Jack53416/SoundLocalization/docs/pictures/ClientGuiDiagram.png

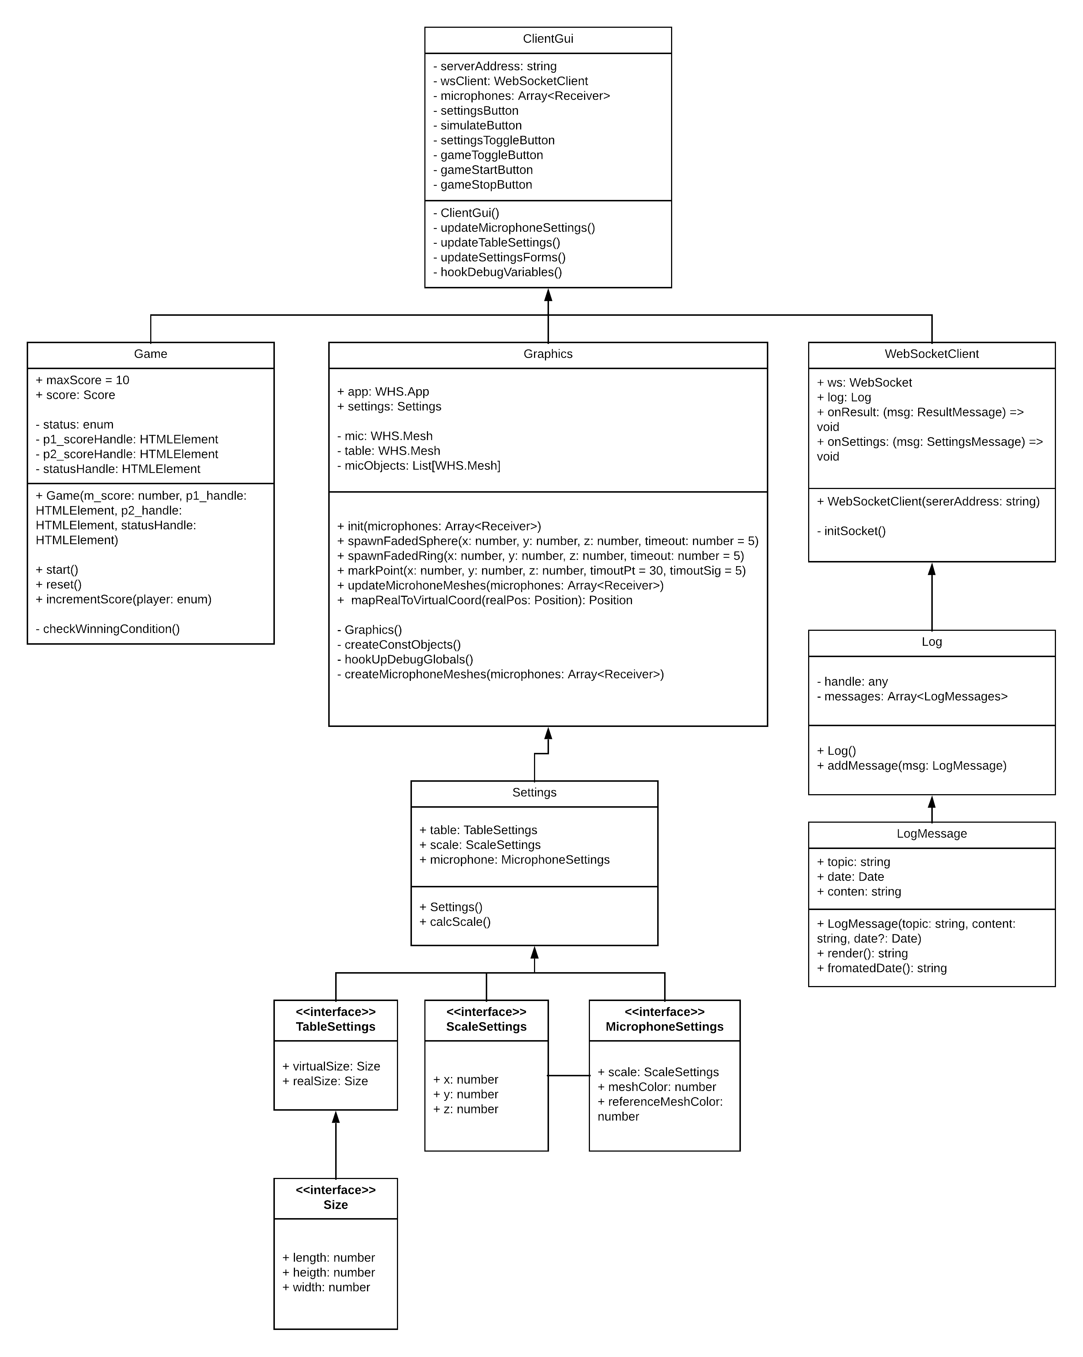
docs/pictures/ClientGuiDiagram.png
