Jack53416/SoundLocalization/docs/pictures/Device diagramV2.png

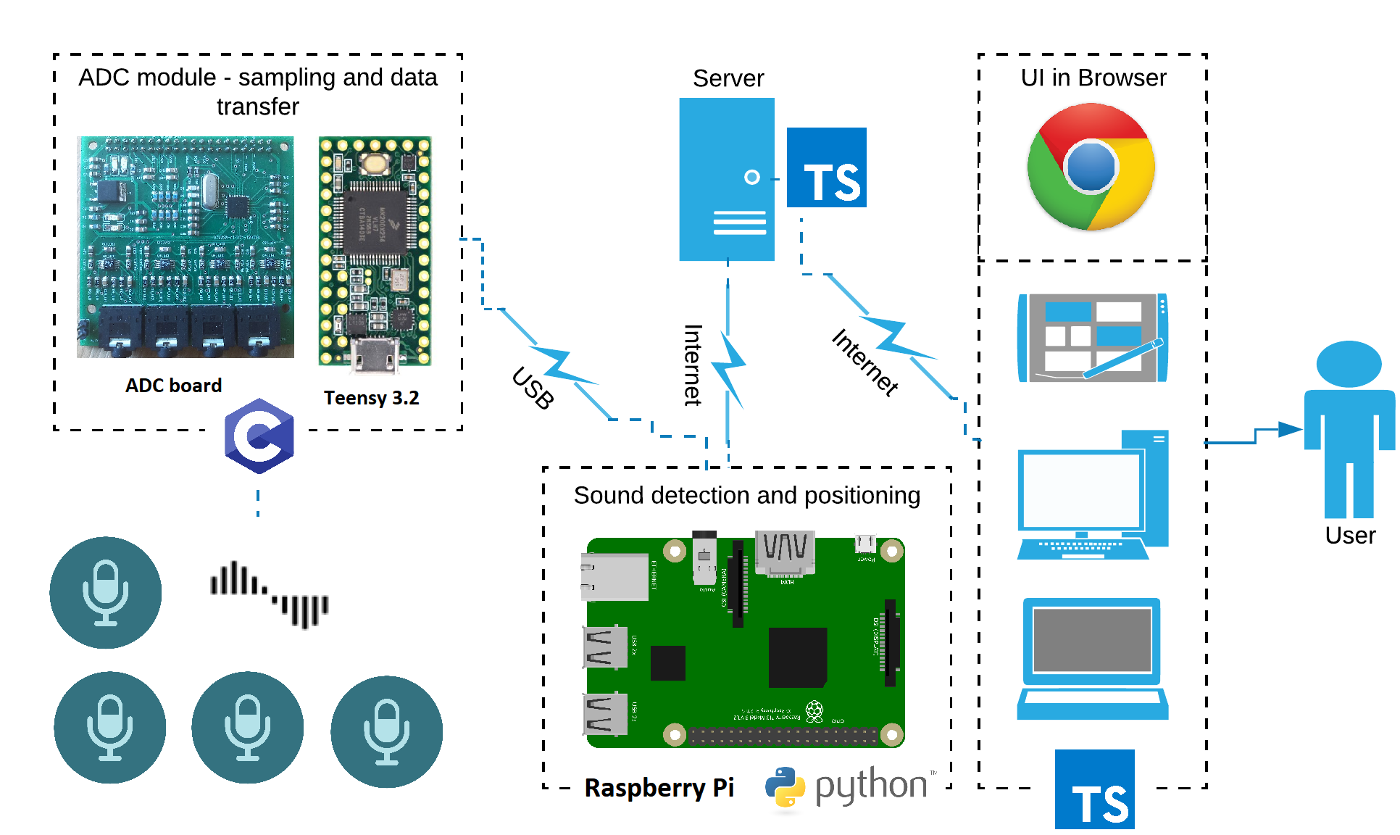
docs/pictures/Device diagramV2.png
