Jack53416/SoundLocalization/docs/pictures/gui-options.PNG

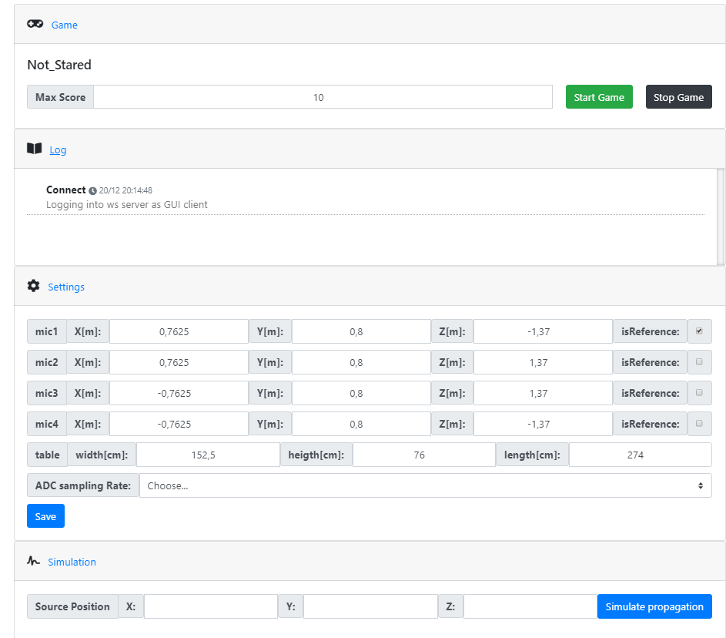
docs/pictures/gui-options.PNG
