Jack53416/SoundLocalization/docs/pictures/GUI.PNG

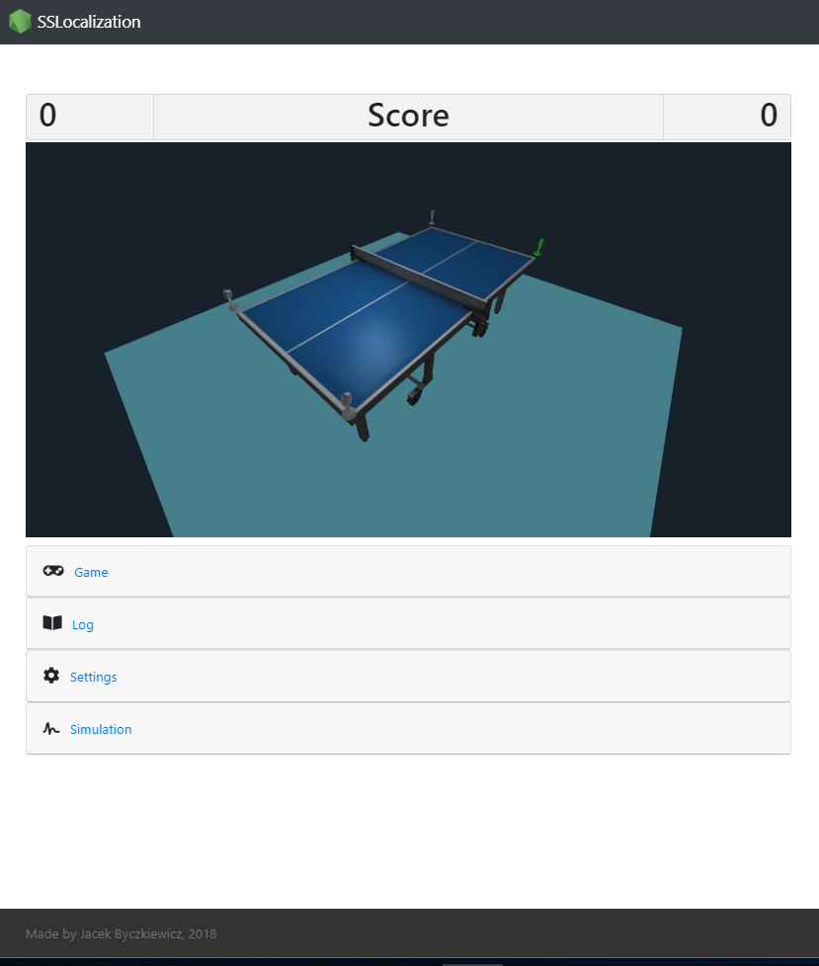
docs/pictures/GUI.PNG
