Jack53416/SoundLocalization/docs/pictures/IncomingMessagesDiagram.png

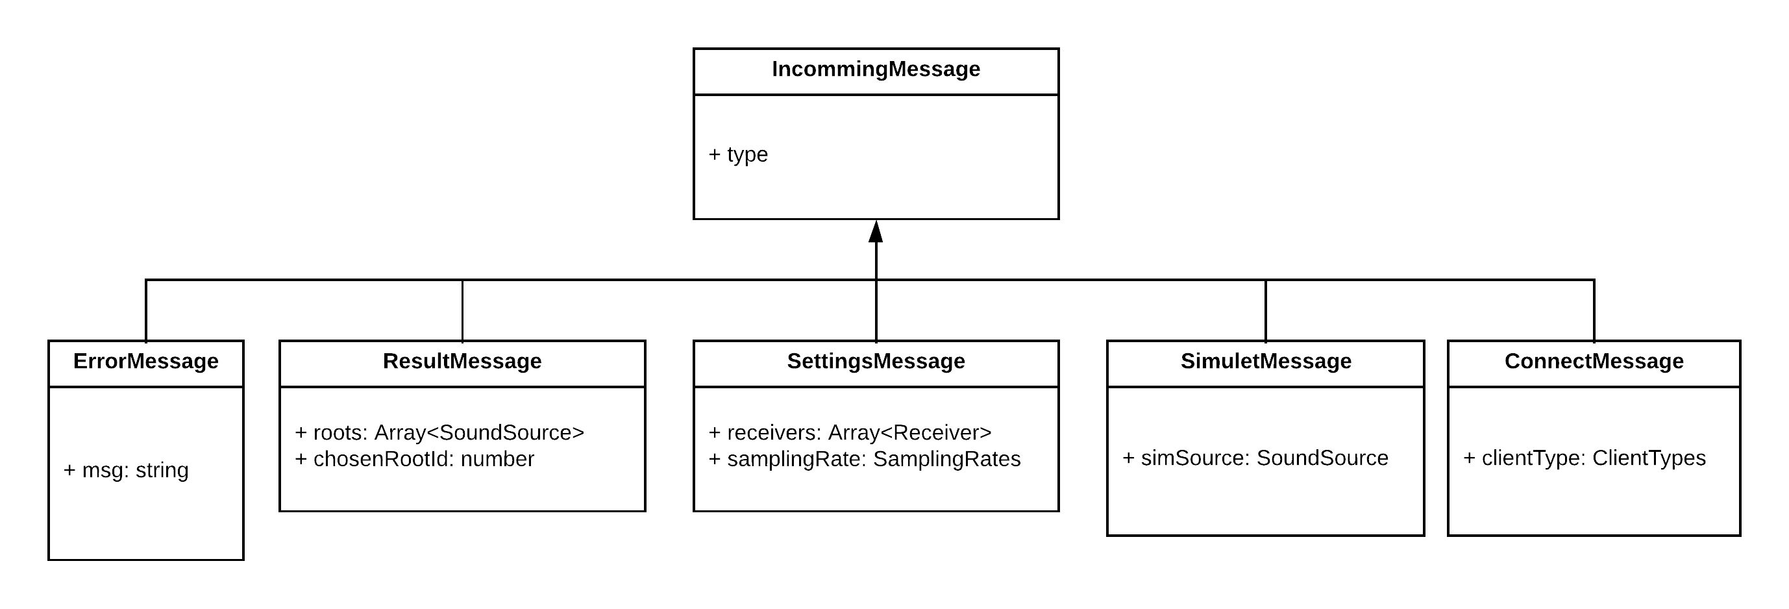
docs/pictures/IncomingMessagesDiagram.png
