Jack53416/SoundLocalization/docs/pictures/plytkaReal2.jpg

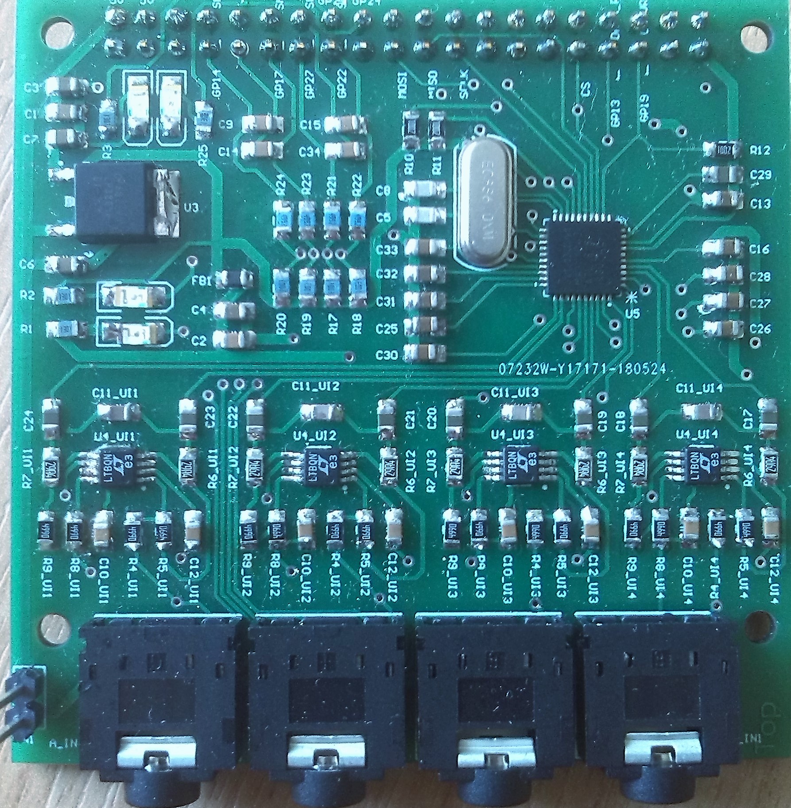
docs/pictures/plytkaReal2.jpg
