Jack53416/SoundLocalization/docs/pictures/ServerDiagram.png

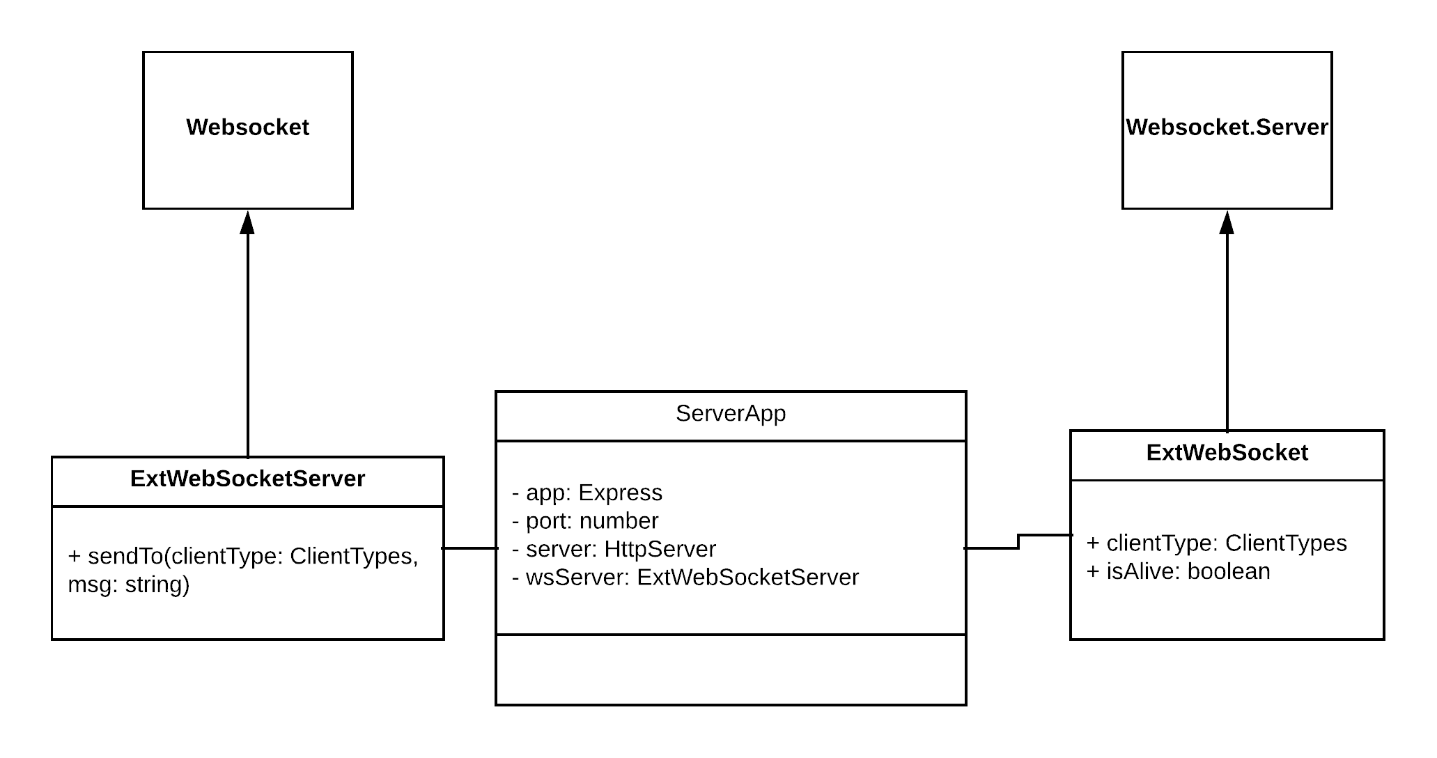
docs/pictures/ServerDiagram.png
