Jack53416/SoundLocalization/docs/pictures/signal.png

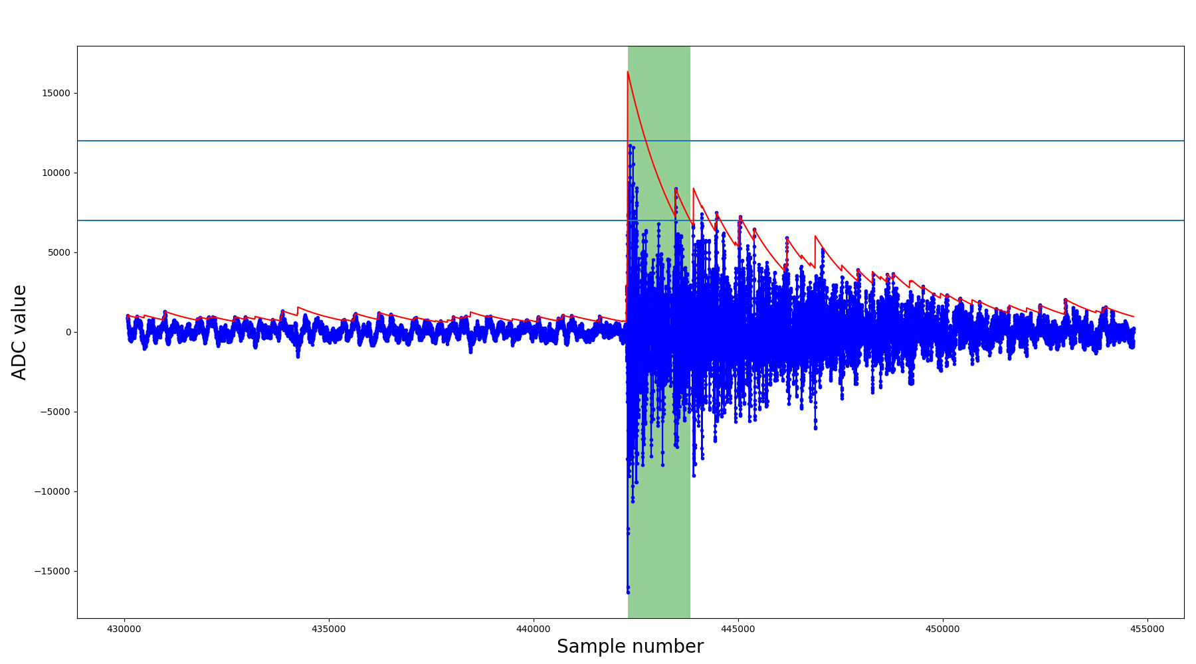
docs/pictures/signal.png
