Jack53416/SoundLocalization/docs/pictures/square_simulation.png

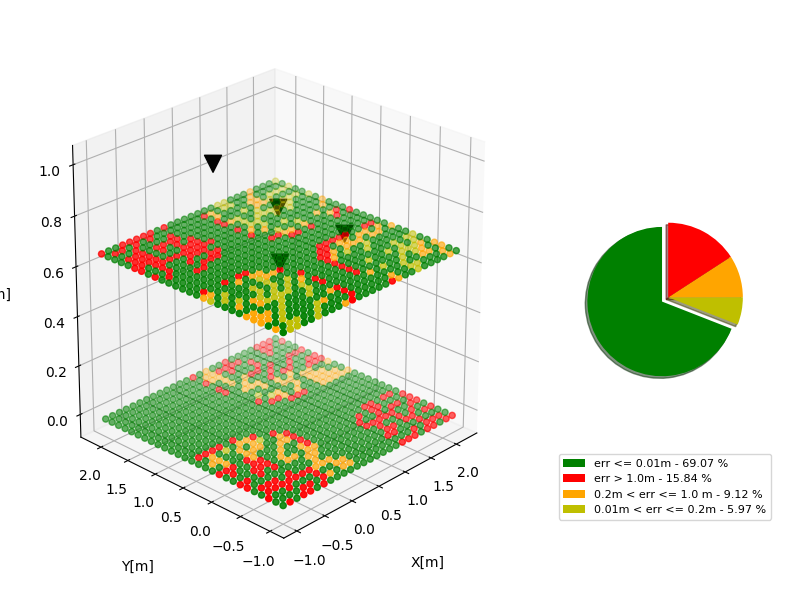
docs/pictures/square_simulation.png
