Jack53416/SoundLocalization/docs/pictures/results_2D_plot.png

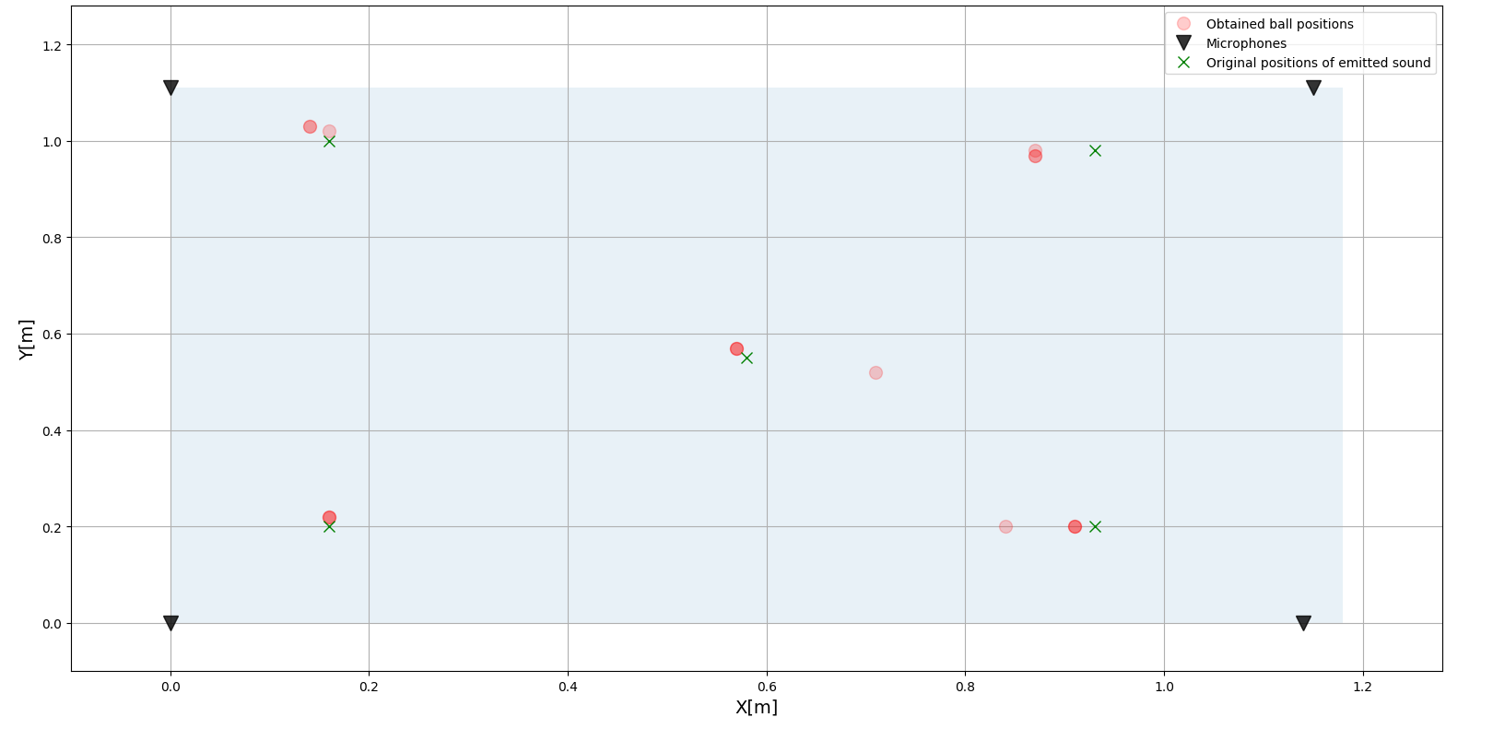
docs/pictures/results_2D_plot.png
